4jakers18/BumpyBot-Battery-Monitor/PCB/BumpyBotBatteryMonitorkicad_pro.kicad_sch

## KiCad design PCB/BumpyBotBatteryMonitorkicad_pro.kicad_sch (2023-10-15)

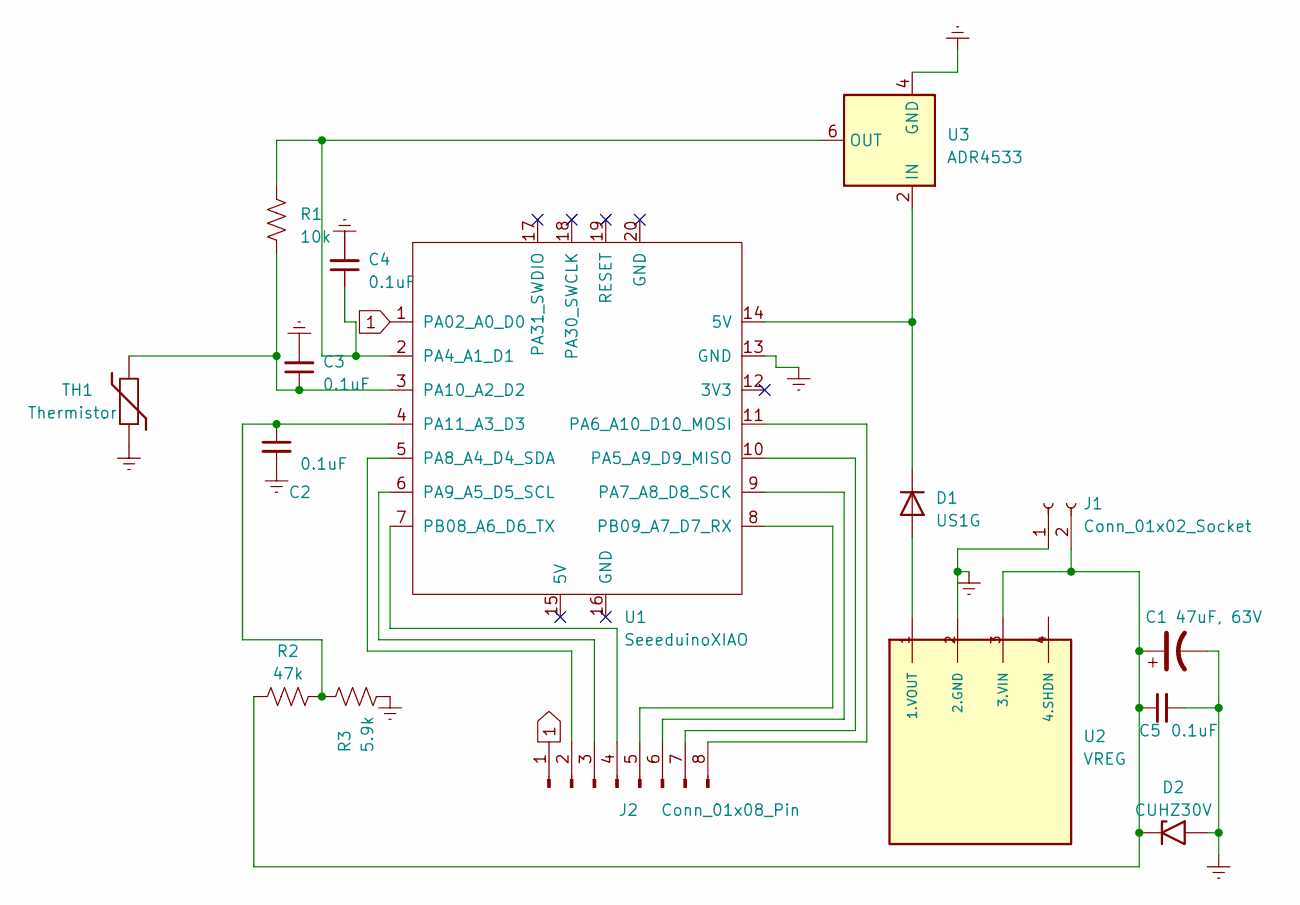
[picture p7: schematic BumpyBotBatteryMonitorkicad_pro.kicad_sch]

Parts:
C1: 47uF, 63V; CP_Axial_L10.0mm_D6.0mm_P15.00mm_Horizontal
C2, C3, C4, C5: 0.1uF; C_0603_1608Metric_Pad1.08x0.95mm_HandSolder
D1: US1G; D_SMA_Handsoldering
D2: CUHZ30V; D_SOD-323_HandSoldering
J1: Conn_01x02_Socket; JST_XH_S2B-XH-A_1x02_P2.50mm_Horizontal
J2: Conn_01x08_Pin; PinHeader_1x08_P2.54mm_Horizontal
R1: 10k; R_0805_2012Metric_Pad1.20x1.40mm_HandSolder
R2: 47k; R_Axial_DIN0411_L9.9mm_D3.6mm_P12.70mm_Horizontal
R3: 5.9k; R_Axial_DIN0207_L6.3mm_D2.5mm_P7.62mm_Horizontal
TH1: Thermistor; JST_XH_S2B-XH-A_1x02_P2.50mm_Horizontal
U1: SeeeduinoXIAO; Seeeduino XIAO-MOUDLE14P-2.54-21X17.8MM
U2: VREG
U3: ADR4533; SOIC-8_3.9x4.9mm_P1.27mm

Connections:
1: J2.1, U1.1 (PA02_A0_D0)
GNDREF: C1.2, C2.2, C3.2, C4.2, C5.2, D2.2 (A2), J1.1, R3.2, TH1.1, U1.13 (GND), U2.2 (2.GND), U3.4 (GND)
unnamed: C1.1, C5.1, D2.1 (A1), J1.2, R2.1, U2.3 (3.VIN)
unnamed: C2.1, R2.2, R3.1, U1.4 (PA11_A3_D3)
unnamed: C3.1, R1.2, TH1.2, U1.3 (PA10_A2_D2)
unnamed: C4.1, R1.1, U1.2 (PA4_A1_D1), U3.6 (OUT)
unnamed: D1.1 (K), U1.14 (5V), U3.2 (IN)
unnamed: D1.2 (A), U2.1 (1.VOUT)
unnamed: J2.2, U1.5 (PA8_A4_D4_SDA)
unnamed: J2.3, U1.6 (PA9_A5_D5_SCL)
unnamed: J2.4, U1.7 (PB08_A6_D6_TX)
unnamed: J2.5, U1.8 (PB09_A7_D7_RX)
unnamed: J2.6, U1.9 (PA7_A8_D8_SCK)
unnamed: J2.7, U1.10 (PA5_A9_D9_MISO)
unnamed: J2.8, U1.11 (PA6_A10_D10_MOSI)
